IboschTonosch/atx-to-lab/KiCAD/ATX_PSU_525W_ENERMAX/ATX_PSU_525W_ENERMAX.sch

## KiCad design KiCAD/ATX_PSU_525W_ENERMAX/ATX_PSU_525W_ENERMAX.sch (2022-02-28)

Schematic: ATX_PSU_525W_ENERMAX.sch

Parts:
C1, C3, C4, C7, C8: 1nF; C_0603_1608Metric_Pad1.05x0.95mm_HandSolder
C2, C5, C6, C9, C10: 0.1uF; C_0603_1608Metric_Pad1.05x0.95mm_HandSolder
DZ1, DZ2, DZ3, DZ4, DZ5: D_Zener_ALT; D_SMC_Handsoldering
F1, F2, F3, F4, F5: 10A; Fuseholder_Cylinder-6.3x32mm_Schurter_0031-8002_Horizontal_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; DigiKey_Nr 486-3322-ND / 486-3643-ND
HS1: Heatsink; Heatsink_Stonecold_HS-132_32x14mm_2xFixation1.5mm
J1, J28, J29: Fan1; Molex_KK-254_AE-6410-02A_1x02_P2.54mm_Vertical
J2: Power On Switch; Molex_KK-254_AE-6410-02A_1x02_P2.54mm_Vertical
J3: Standby LED; Molex_KK-254_AE-6410-02A_1x02_P2.54mm_Vertical
J4: EPS12V 4Pin; Molex_Mini-Fit_Jr_5566-04A_2x02_P4.20mm_Vertical
J5, J15, J16, J30, J31: Potti; Molex_KK-254_AE-6410-03A_1x03_P2.54mm_Vertical
J6, J17, J18: LED Yellow; Molex_KK-254_AE-6410-02A_1x02_P2.54mm_Vertical
J7, J19, J21, J34, J36: Volt Sens; Molex_KK-254_AE-6410-02A_1x02_P2.54mm_Vertical
J8, J20, J22: 12V Out; Altech_AK300_1x02_P5.00mm_45-Degree
J9: Main ATX 24Pin; Molex_Mini-Fit_Jr_5566-24A_2x12_P4.20mm_Vertical
J10: EPS12V 8 Pin; Molex_Mini-Fit_Jr_5566-12A_2x06_P4.20mm_Vertical; Digi-Key WM3811-ND
J11, J24, J25, J40, J41: Current Sens; Molex_KK-254_AE-6410-03A_1x03_P2.54mm_Vertical
J12, J14, J27: Molex: 0039281243; Molex_Mini-Fit_Jr_5566-08A_2x04_P4.20mm_Vertical; Digi-Key WM3811-ND
J13, J26: Molex: 0039281243; Molex_Mini-Fit_Jr_5566-12A_2x06_P4.20mm_Vertical; Digi-Key WM3811-ND
J23: Molex: 0039281243; Molex_Mini-Fit_Jr_5566-08A2_2x04_P4.20mm_Vertical; Digi-Key WM3811-ND
J32: LED Red; Molex_KK-254_AE-6410-02A_1x02_P2.54mm_Vertical
J33: LED Orange; Molex_KK-254_AE-6410-02A_1x02_P2.54mm_Vertical
J35: 5V Out; Altech_AK300_1x02_P5.00mm_45-Degree
J37: 3.3V Out; Altech_AK300_1x02_P5.00mm_45-Degree
J38, J39, J42, J43: Screw_Terminal_01x06; TerminalBlock_RND_205-00005_1x06_P5.00mm_Horizontal
J44: Screw_Terminal_01x12; TerminalBlock_RND_205-00011_1x12_P5.00mm_Horizontal
Q1, Q2, Q3, Q4, Q5: Q_NMOS_DGS; TO-220-3_Vertical; DigiKey_Nr SUP10250E-GE3-ND
R1, R4, R5: 680; R_Axial_DIN0516_L15.5mm_D5.0mm_P20.32mm_Horizontal
R2: 20; R_Axial_Power_L20.0mm_W6.4mm_P25.40mm
R3, R6, R8, R10, R12: 1k; R_Axial_DIN0516_L15.5mm_D5.0mm_P20.32mm_Horizontal
R7: 680; R_Axial_Power_L20.0mm_W6.4mm_P25.40mm
R9: 300; R_Axial_DIN0516_L15.5mm_D5.0mm_P20.32mm_Horizontal
R11: 20; R_Axial_DIN0516_L15.5mm_D5.0mm_P20.32mm_Horizontal
U1, U2, U3, U4, U5: ACS712xLCTR-20A; SOIC-8_3.9x4.9mm_P1.27mm

Notes on the sheet:
Primary +12V1 Power Rail Input Terminal
Secondary +12V2/+12V3 Power Rail Input Terminal
Secondary +5V Power Input Terminal
Secondary +12V3 Power Rail Input Terminal
Connect a swst switch. The switch will short the PS_ON connector with the Ground and start the power supply. When using a switch with LED lighting then use a one of the power rails to power the led seperately and put a pull-up resistor into your led circuit.
Connect a LED as an standby indicator. Do not use this connection for high power circuits.
Power On/Off Connection
Standby Indicator
The heatsink will be attached to the power mosfets.
Mosfet Cooling
Secondary +12V2 Power Rail Input Terminal
These pins will not be used in the power supply
